aentinger/RelayChildboard/images/relay-childboard-top-large.jpg

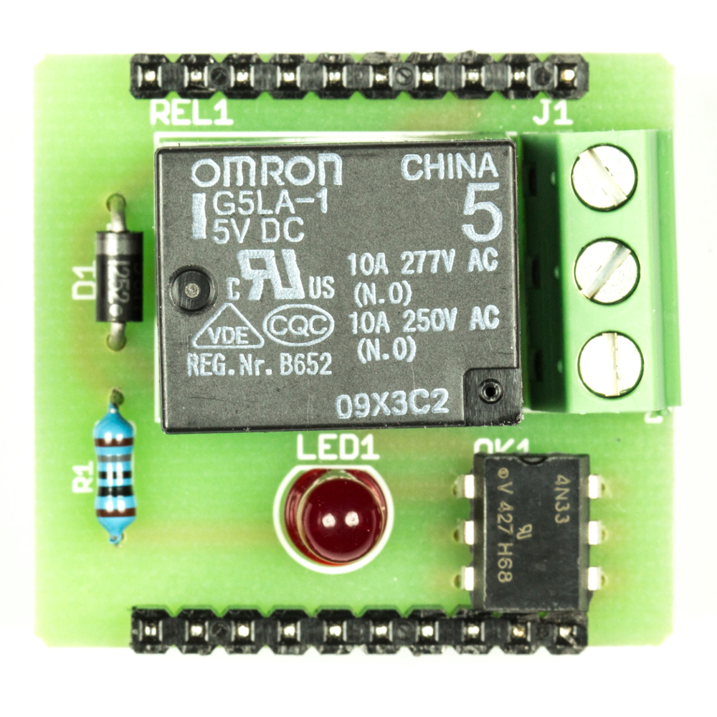
images/relay-childboard-top-large.jpg
